dgschwend/sunrise-clock/Documentation/Dimmer Module (not used)/lichtwecker-1.png

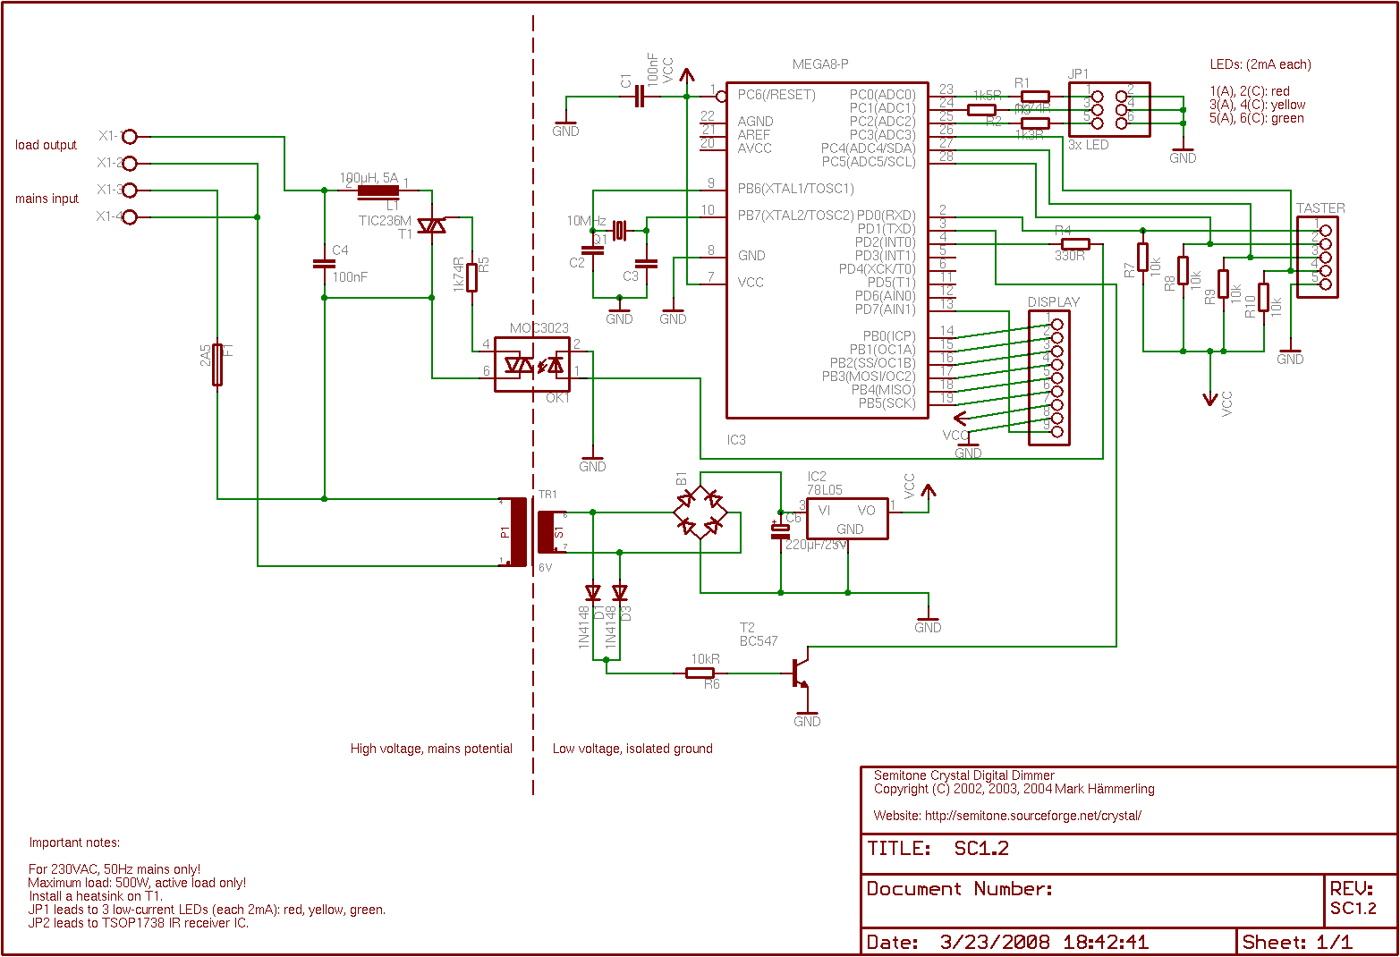
Documentation/Dimmer Module (not used)/lichtwecker-1.png
