dgschwend/sunrise-clock/Documentation/Dimmer Module (not used)/phasenanschnittsdimmer.jpg

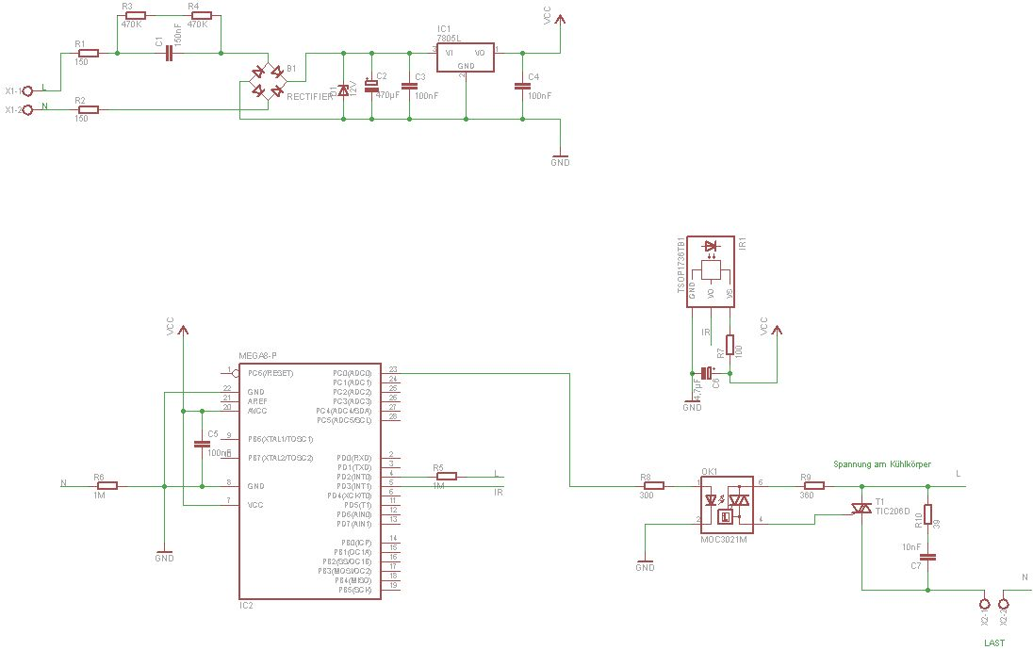
Documentation/Dimmer Module (not used)/phasenanschnittsdimmer.jpg
