dgschwend/sunrise-clock/Documentation/Photos/rtc.jpg

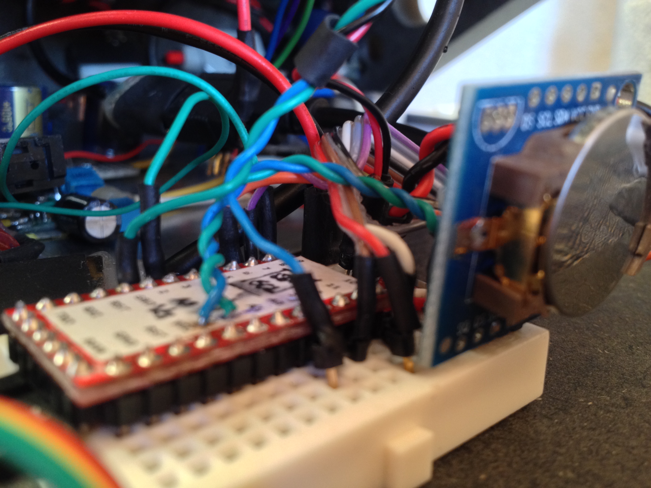
Documentation/Photos/rtc.jpg
