dgschwend/sunrise-clock/AudioBoard PCB/Outputs/Final Artwork.PDF

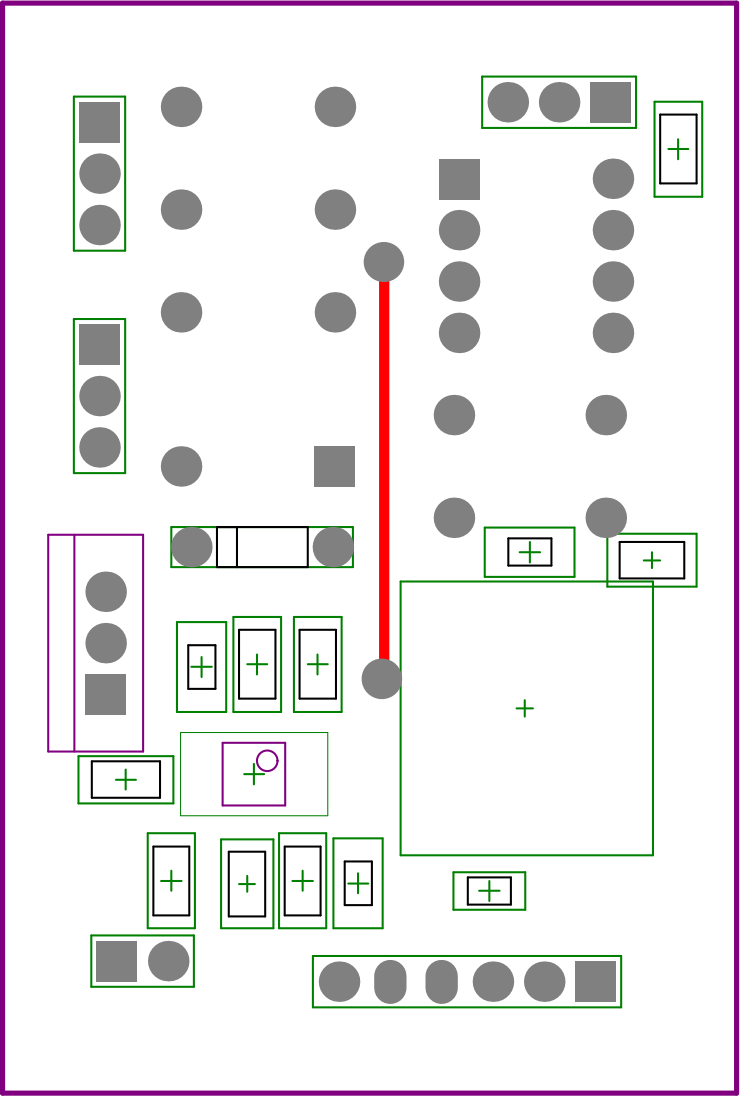
[picture p48: page 1]

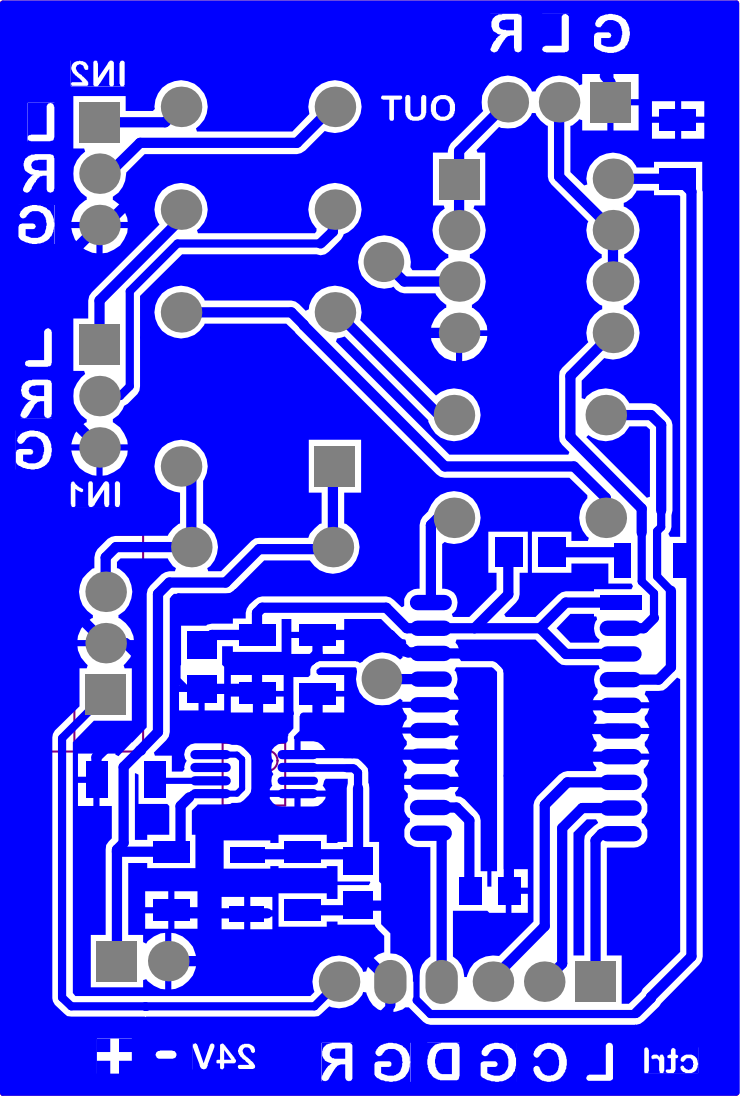
[picture p49: page 2]

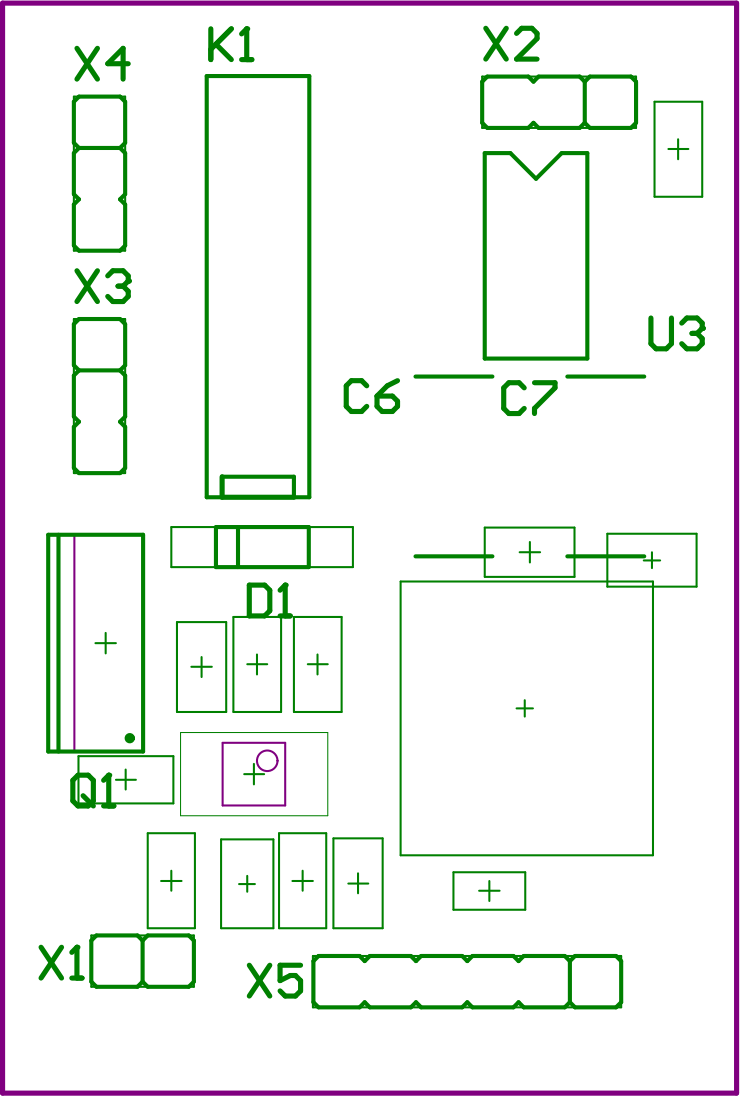
[picture p50: page 3]

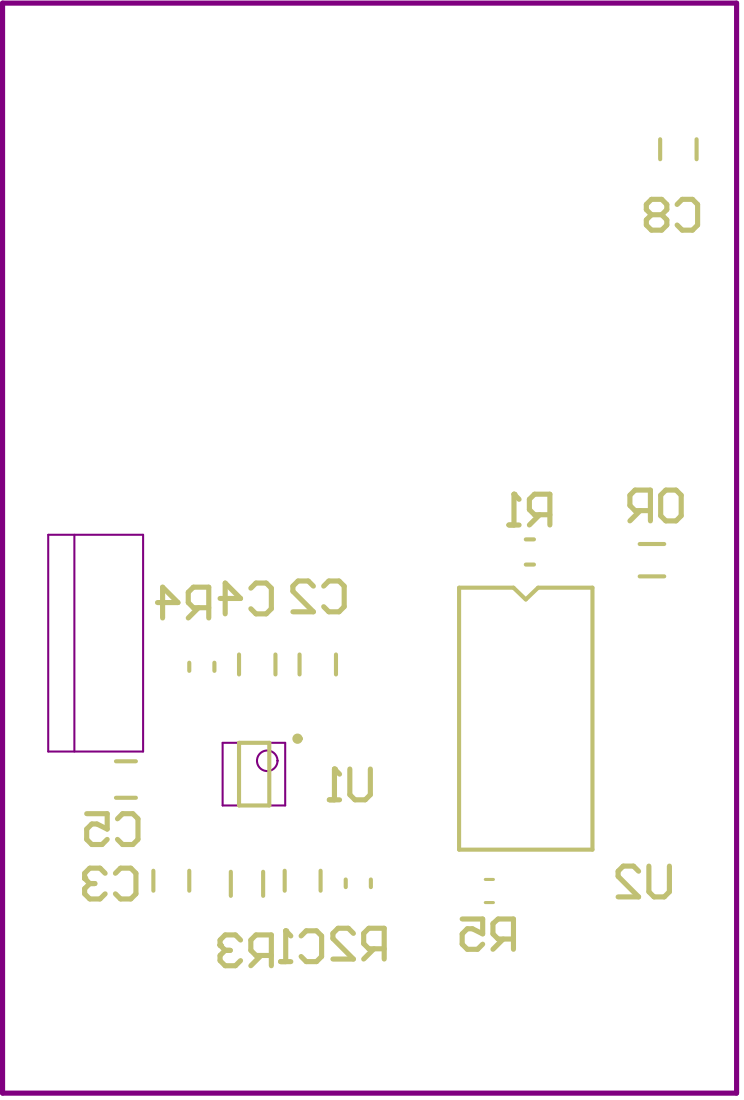
[picture p51: page 4]

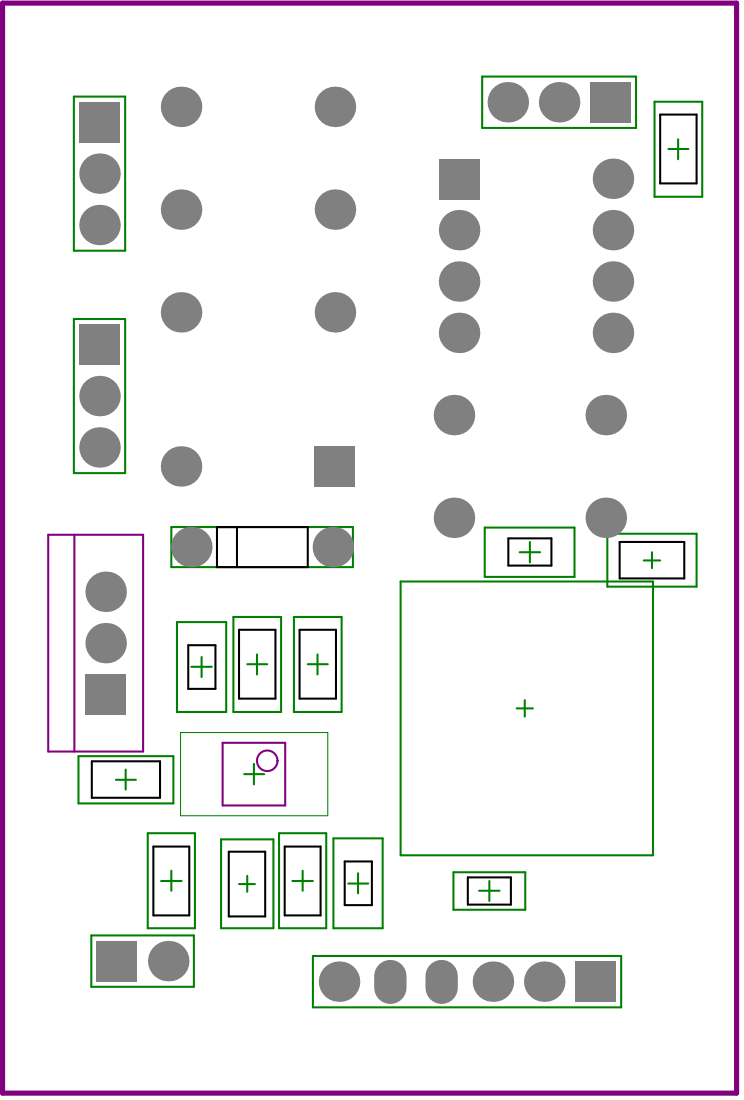
[picture p52: page 5]

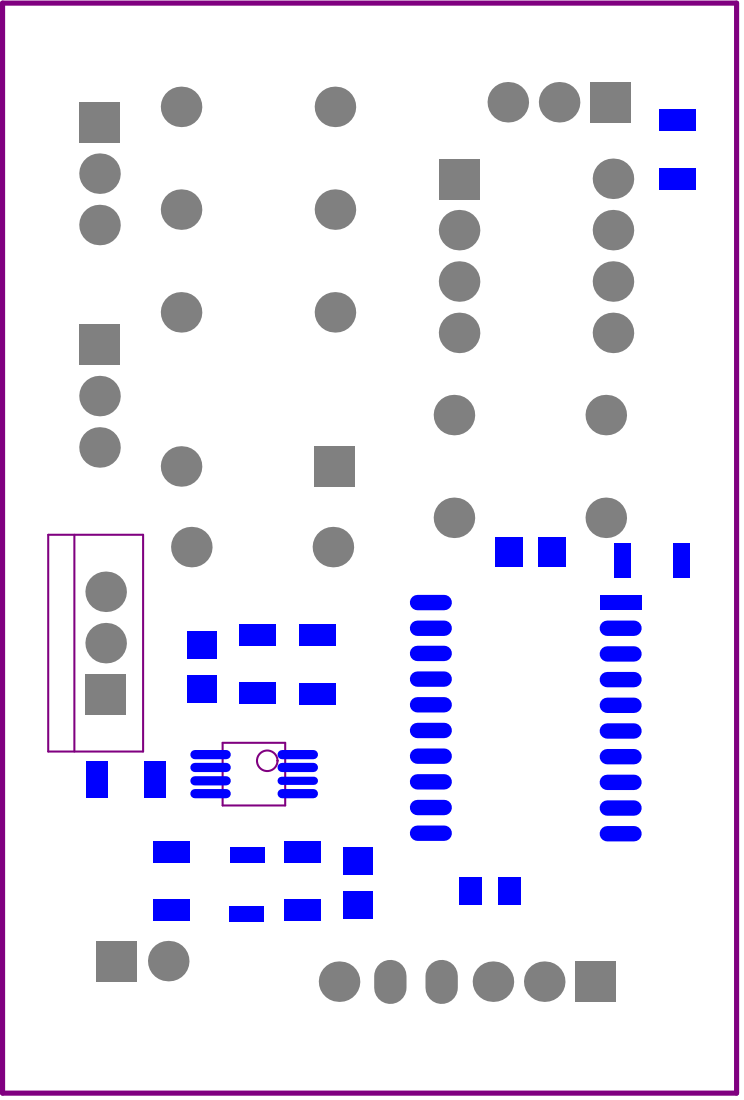
[picture p53: page 6]

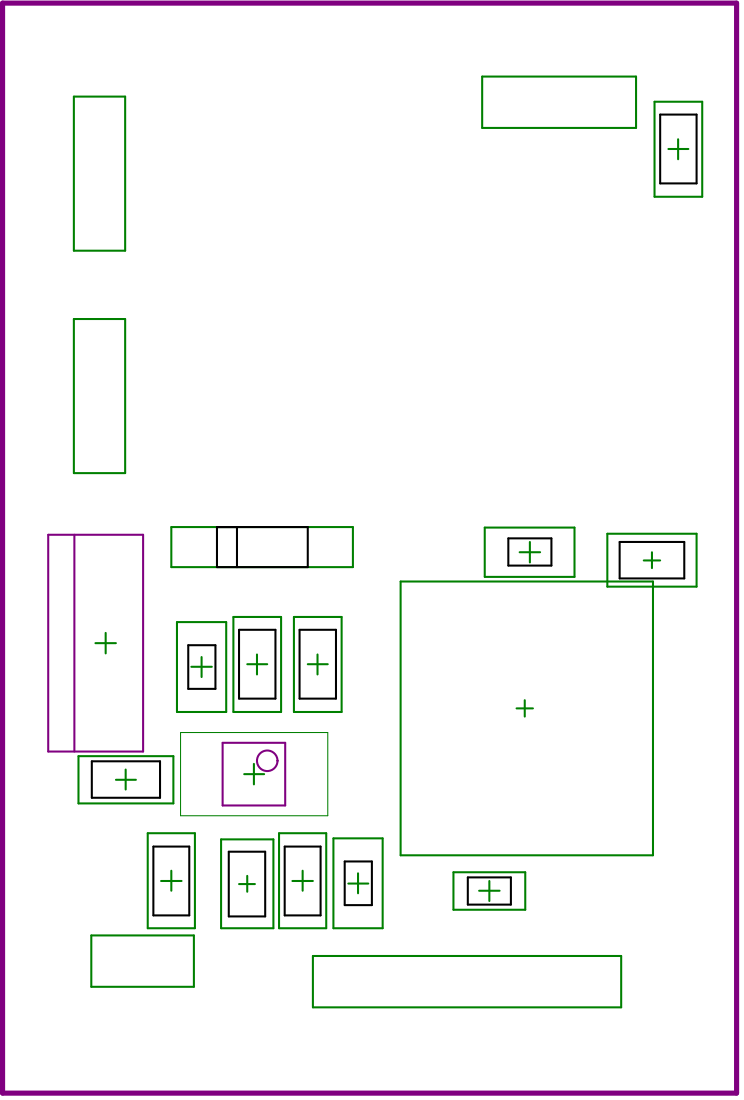
[picture p54: page 7]

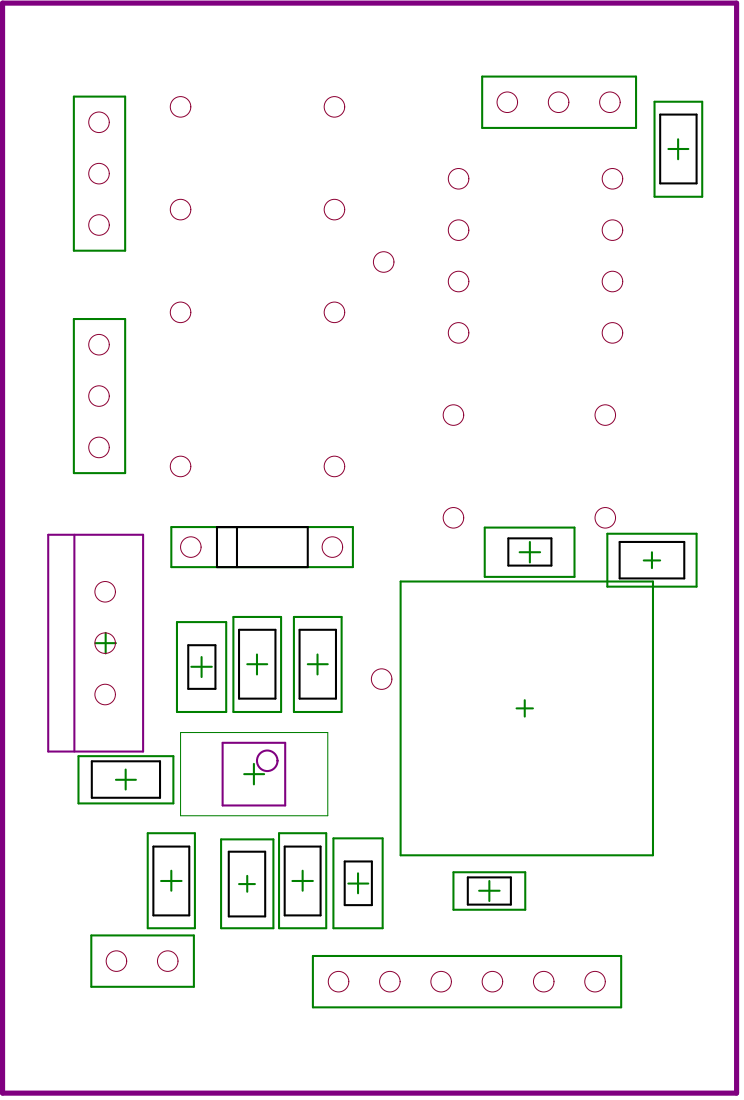
[picture p55: page 8]

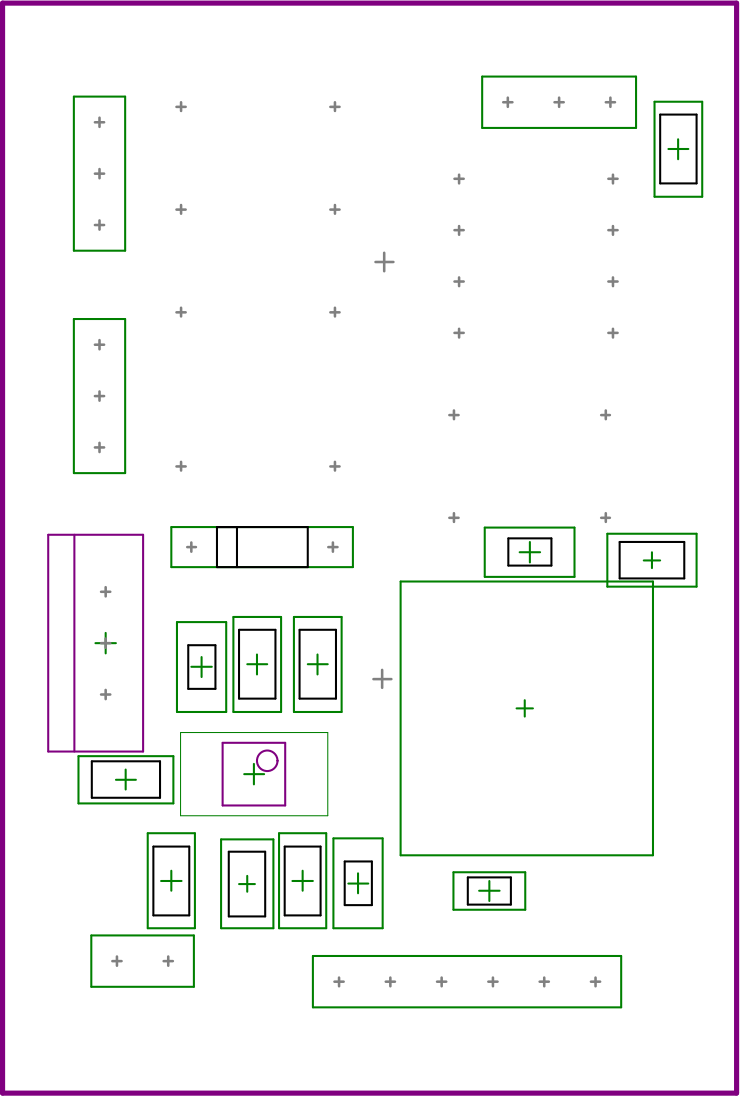
[picture p56: page 9]
