dgschwend/sunrise-clock/AudioBoard PCB/Outputs/PCB 3D Bottom.PDF

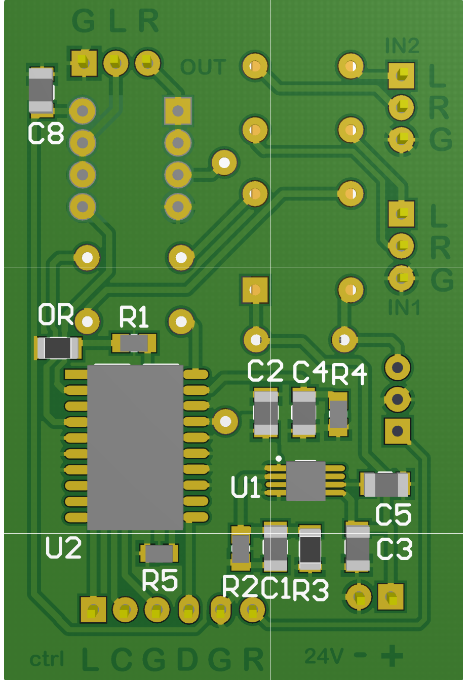
[picture p57: page 1]
