dgschwend/sunrise-clock/AudioBoard PCB/Outputs/PCB 3D Top.PDF

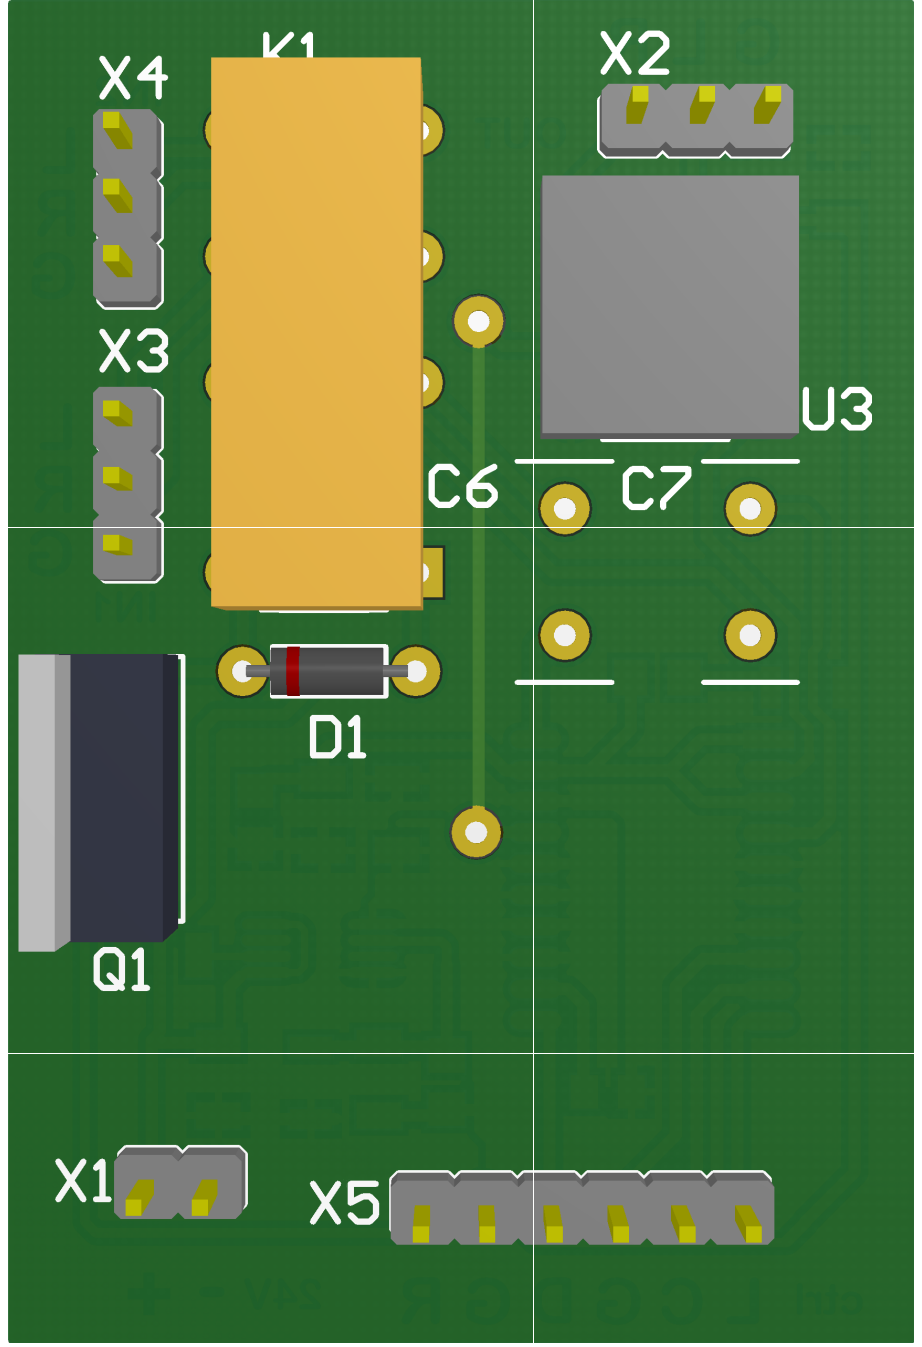
[picture p58: page 1]
