dgschwend/sunrise-clock/AudioBoard PCB/Outputs/Toner Transfer.PDF

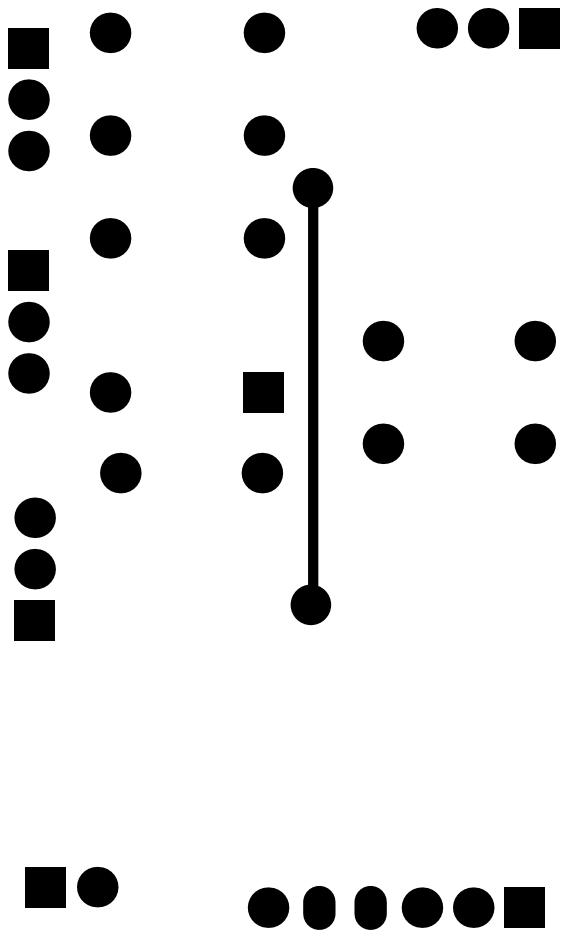
[picture p59: page 1]

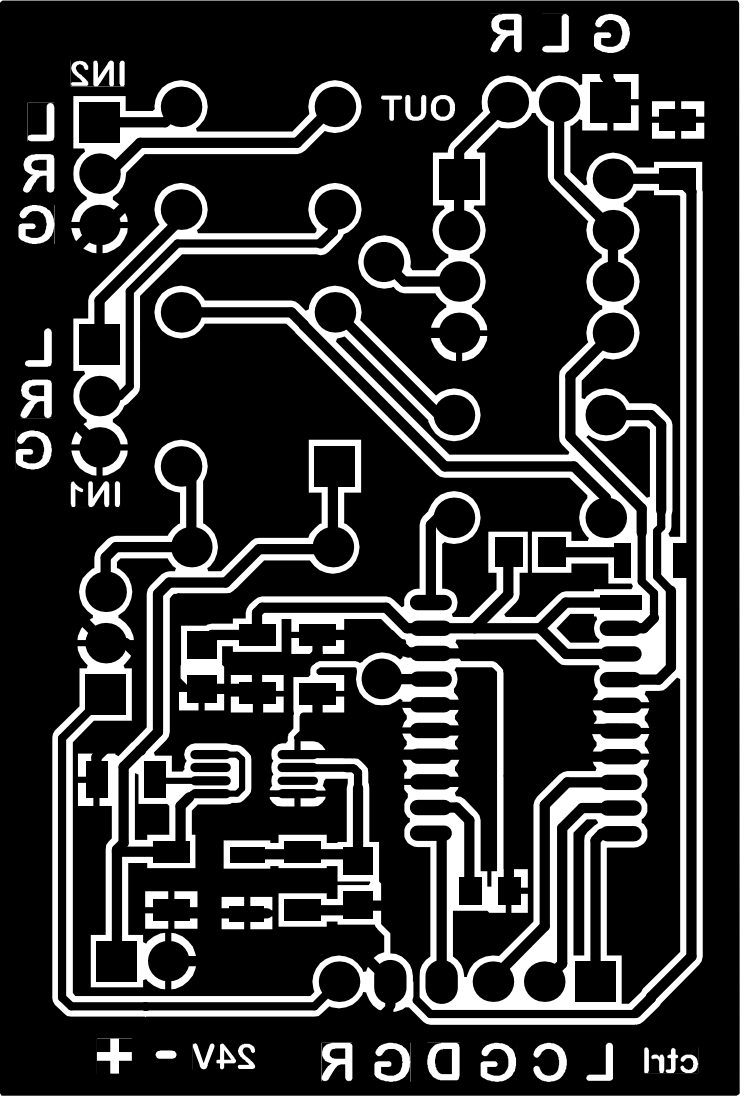
[picture p60: page 2]
