dgschwend/sunrise-clock/LEDMatrix PCB/Outputs/Final Artwork.PDF

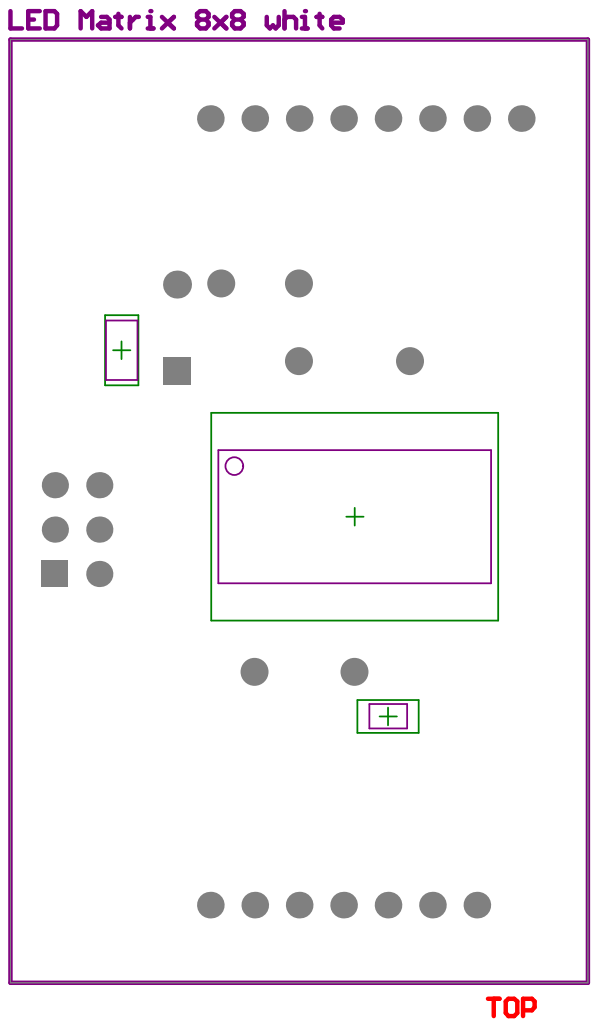
[picture p61: page 1]

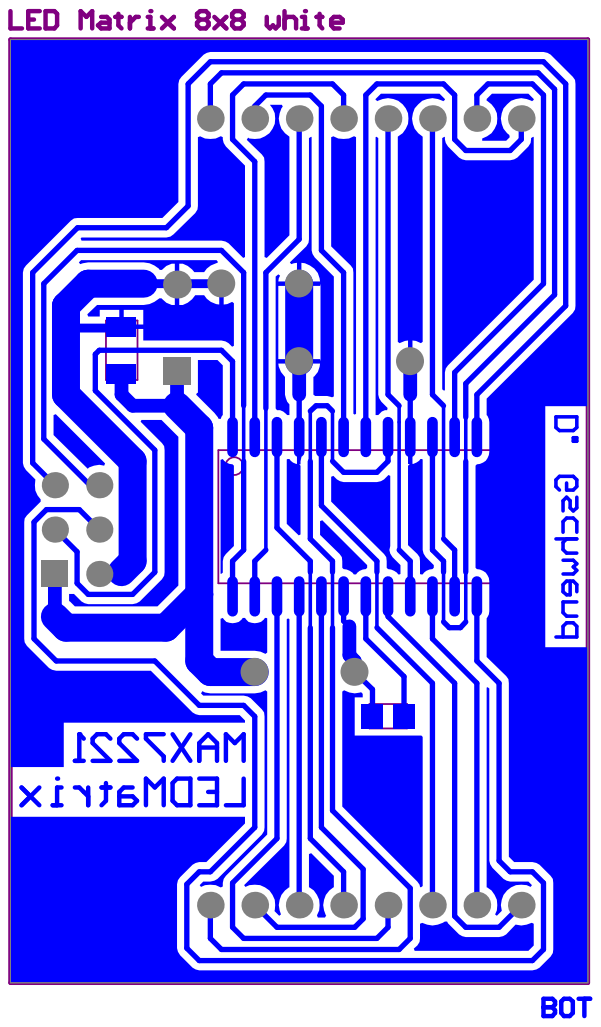
[picture p62: page 2]

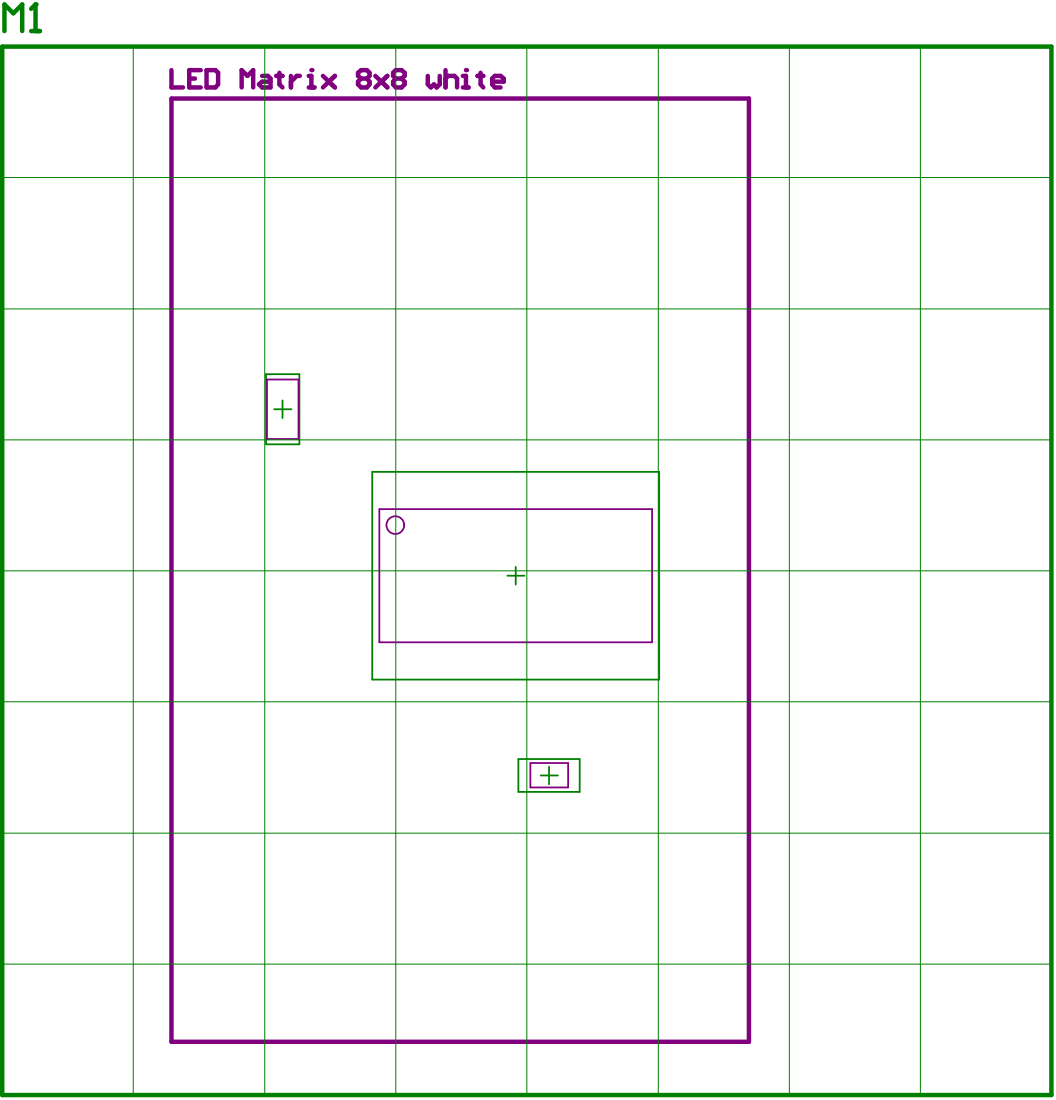
[picture p63: page 3]

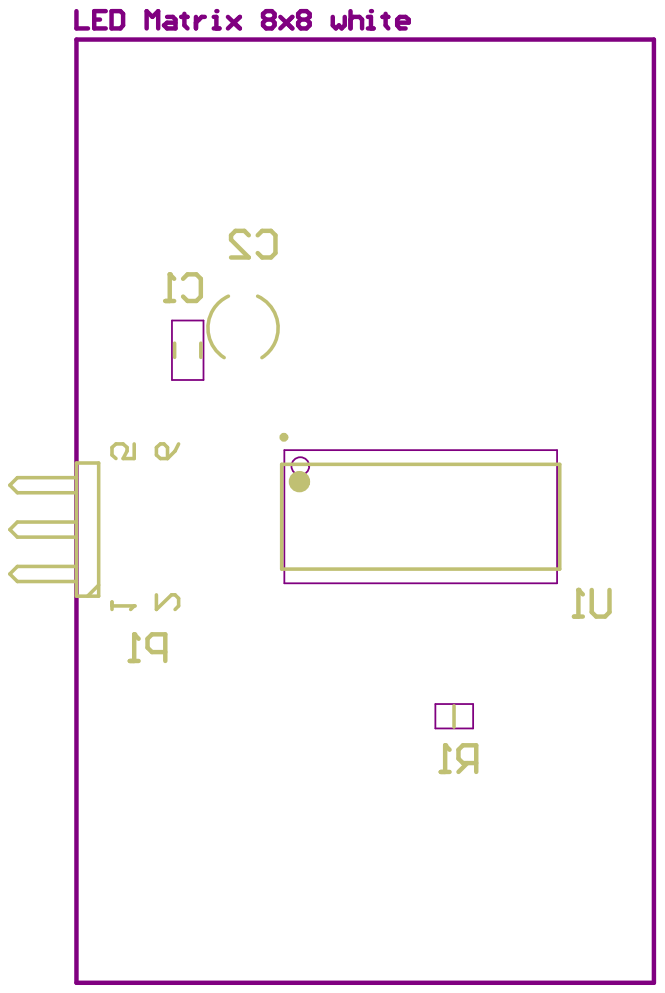
[picture p64: page 4]

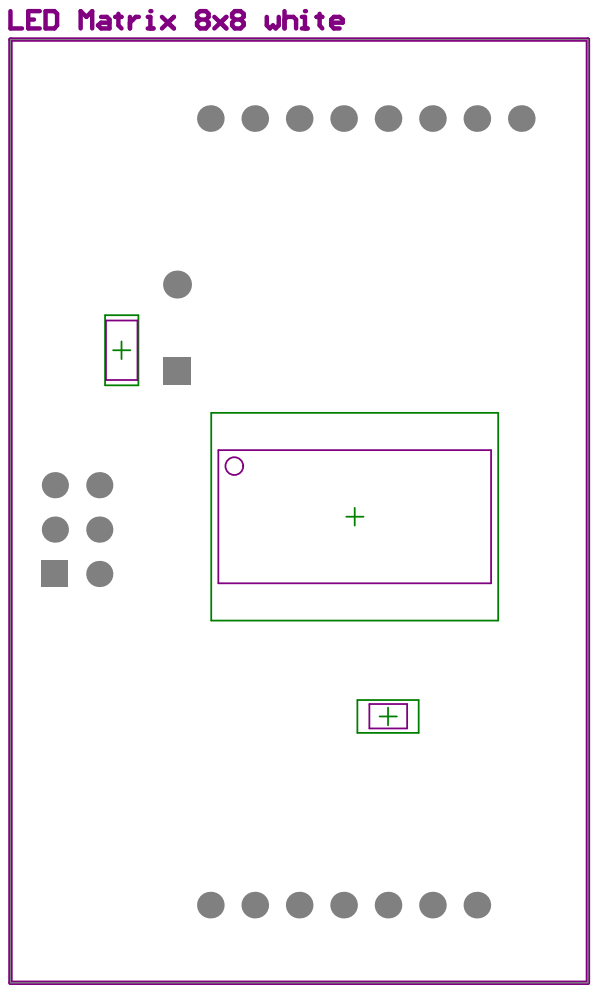
[picture p65: page 5]

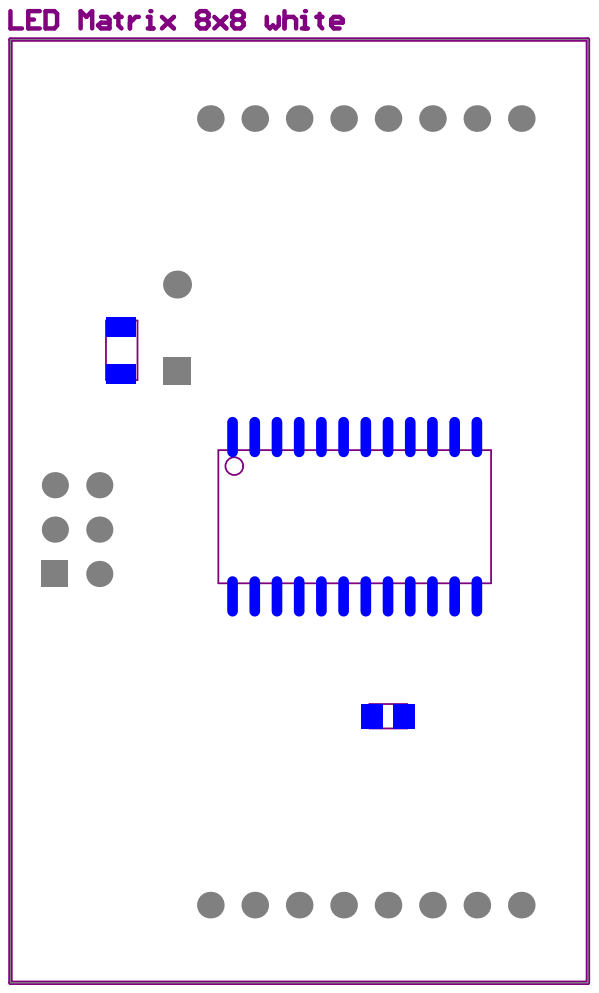
[picture p66: page 6]

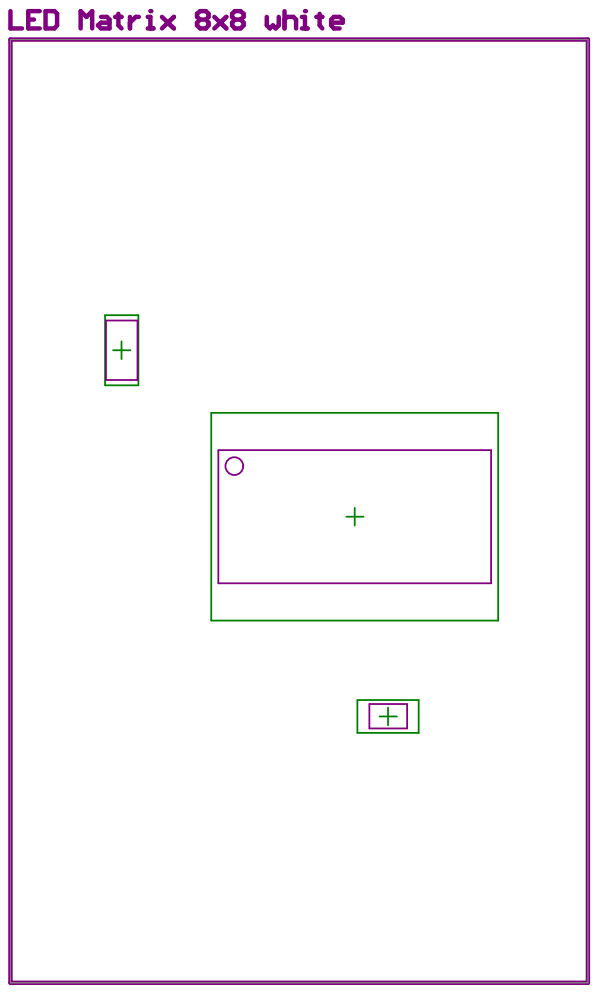
[picture p67: page 7]

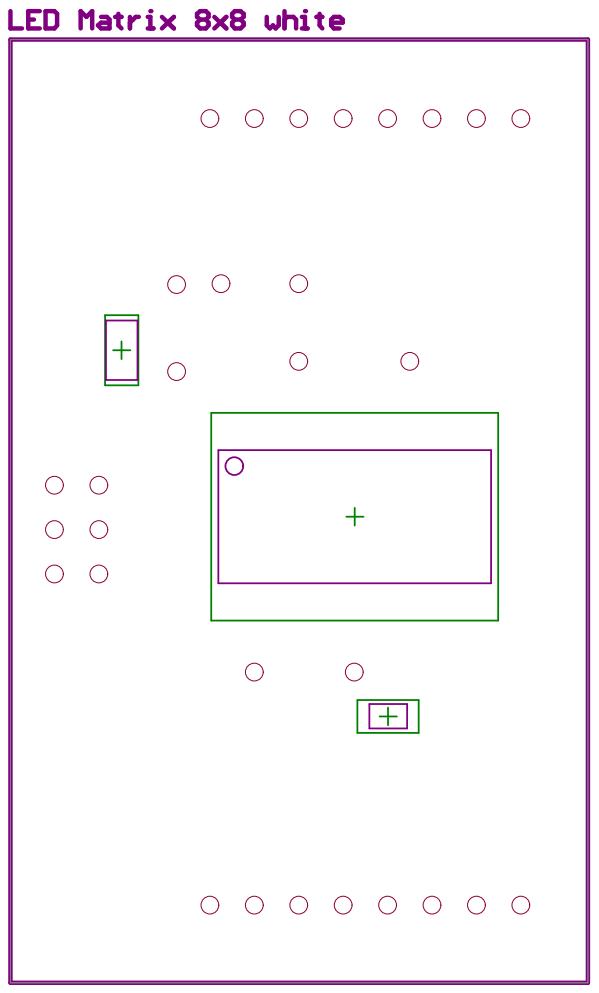
[picture p68: page 8]

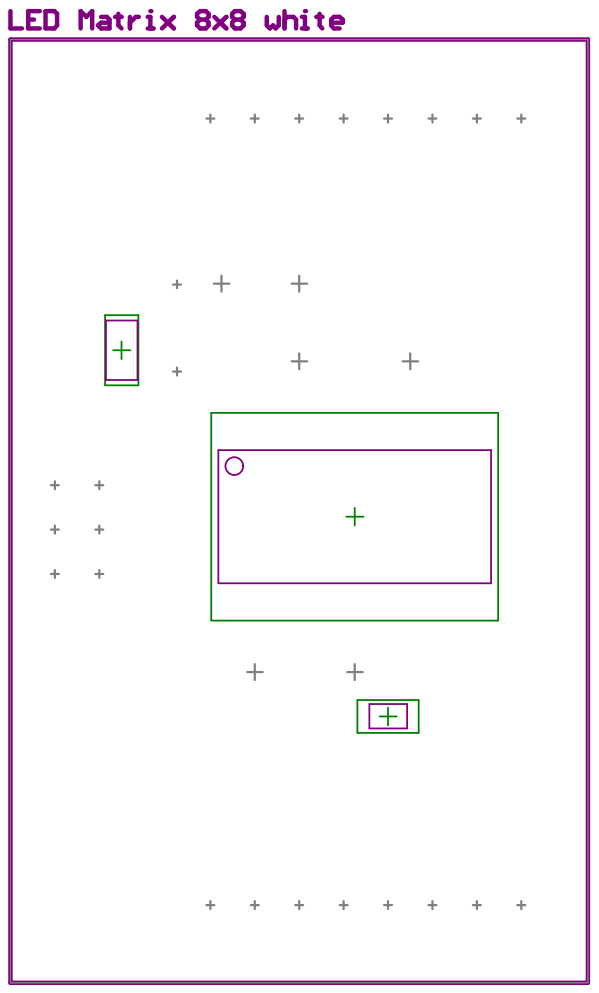
[picture p69: page 9]
