dgschwend/sunrise-clock/LEDMatrix PCB/Outputs/PCB 3D Bottom.PDF

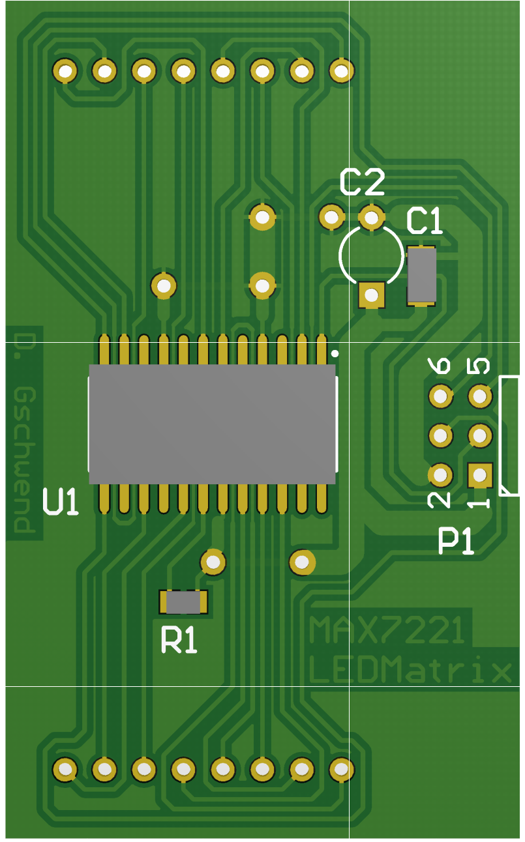
[picture p70: page 1]
