dgschwend/sunrise-clock/LEDMatrix PCB/Outputs/PCB 3D Top.PDF

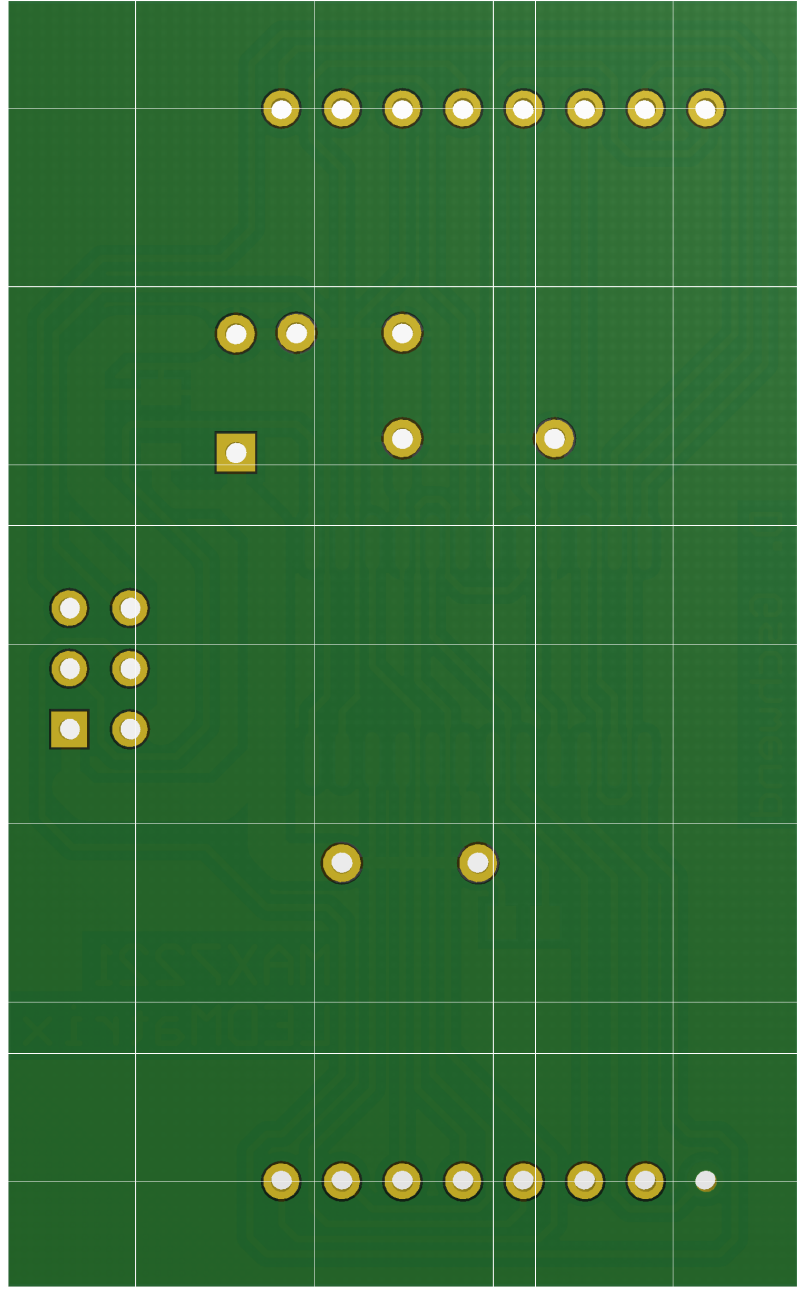
[picture p71: page 1]
